jusdisgi/slimsplaydy/output/outlines/case_inner_wall_left.dxf

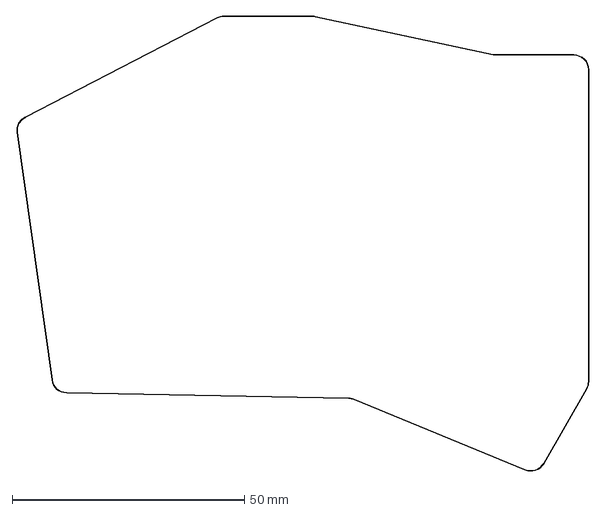
[picture p18: CAD file, 2025-06-13]
output/outlines/case_inner_wall_left.dxf
123.1 x 98.2 mm
