jusdisgi/slimsplaydy/output/outlines/screw_heads.dxf

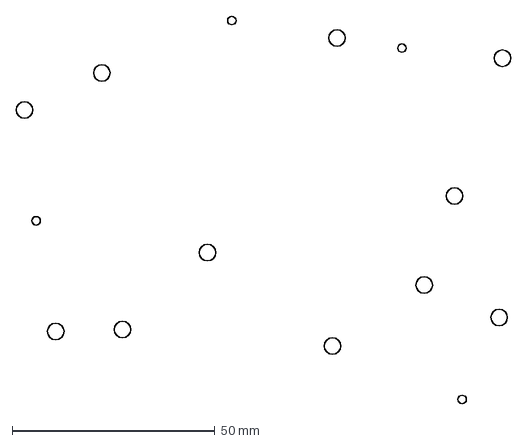
[picture p19: CAD file, 2025-06-14]
output/outlines/screw_heads.dxf
122.0 x 95.6 mm
